remy/midi-to-ps2/scancodes.h

#define SCANCODE_0 0x45
#define SCANCODE_1 0x16
#define SCANCODE_2 0x1E
#define SCANCODE_3 0x26
#define SCANCODE_4 0x25
#define SCANCODE_5 0x2E
#define SCANCODE_6 0x36
#define SCANCODE_7 0x3D
#define SCANCODE_8 0x3E
#define SCANCODE_9 0x46
#define SCANCODE_A 0x1C
#define SCANCODE_BRACKETLEFT 0x54
#define SCANCODE_B 0x32
#define SCANCODE_BACKQUOTE 0x0E
#define SCANCODE_C 0x21
#define SCANCODE_MINUS 0x4E
#define SCANCODE_D 0x23
#define SCANCODE_EQUAL 0x55
#define SCANCODE_E 0x24
#define SCANCODE_BACKSLASH 0x5D
#define SCANCODE_F 0x2B
#define SCANCODE_BACKSPACE 0x66
#define SCANCODE_G 0x34
#define SCANCODE_SPACE 0x29
#define SCANCODE_H 0x33
#define SCANCODE_TAB 0x0D
#define SCANCODE_I 0x43
#define SCANCODE_CAPS 0x58
#define SCANCODE_J 0x3B
#define SCANCODE_SHIFTLEFT 0x12
#define SCANCODE_K 0x42
#define SCANCODE_CONTROLLEFT 0x14
#define SCANCODE_L 0x4B
#define SCANCODE_NUM 0x77
#define SCANCODE_M 0x3A
#define SCANCODE_ALTLEFT 0x11
#define SCANCODE_N 0x31
#define SCANCODE_SHIFTRIGHT 0x59
#define SCANCODE_KP_MUL 0x7C
#define SCANCODE_O 0x44
#define SCANCODE_KP_MINUS 0x7B
#define SCANCODE_P 0x4D
#define SCANCODE_KP_PLUS 0x79
#define SCANCODE_Q 0x15
#define SCANCODE_R 0x2D
#define SCANCODE_KP_PERIOD 0x71
#define SCANCODE_S 0x1B
#define SCANCODE_ENTER 0x5A
#define SCANCODE_KP0 0x70
#define SCANCODE_T 0x2C
#define SCANCODE_ESC 0x76
#define SCANCODE_KP1 0x69
#define SCANCODE_U 0x3C
#define SCANCODE_F1 0x05
#define SCANCODE_KP2 0x72
#define SCANCODE_V 0x2A
#define SCANCODE_F2 0x06
#define SCANCODE_KP3 0x7A
#define SCANCODE_W 0x1D
#define SCANCODE_F3 0x04
#define SCANCODE_KP4 0x6B
#define SCANCODE_X 0x22
#define SCANCODE_F4 0x0C
#define SCANCODE_KP5 0x73
#define SCANCODE_Y 0x35
#define SCANCODE_F5 0x03
#define SCANCODE_KP6 0x74
#define SCANCODE_Z 0x1A
#define SCANCODE_F6 0x0B
#define SCANCODE_KP7 0x6C
#define SCANCODE_F7 0x83
#define SCANCODE_KP8 0x75
#define SCANCODE_F8 0x0A
#define SCANCODE_KP9 0x7D
#define SCANCODE_F9 0x01
#define SCANCODE_BRACKETRIGHT 0x5B
#define SCANCODE_F10 0x09
#define SCANCODE_SEMICOLON 0x4C
#define SCANCODE_F11 0x78
#define SCANCODE_QUOTE 0x52
#define SCANCODE_F12 0x07
#define SCANCODE_COMMA 0x41
#define SCANCODE_PERIOD 0x49
#define SCANCODE_SCROLL 0x7E
#define SCANCODE_SLASH 0x4A
